dekuNukem/traffic-cone-film-scanning/images/dof35mm.png

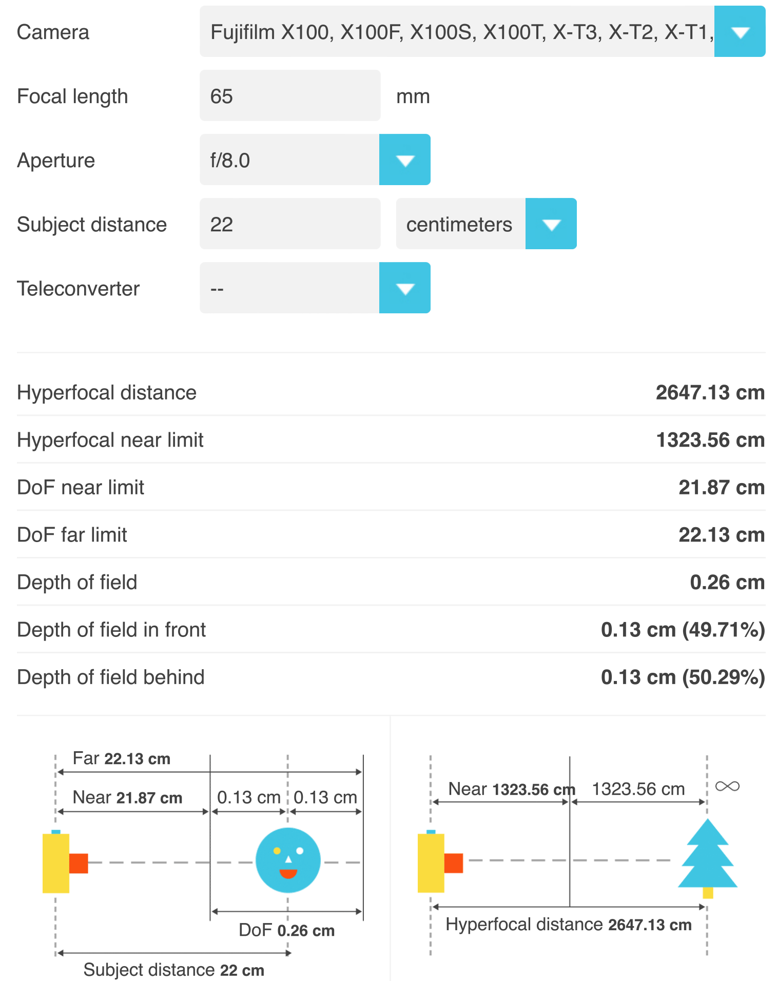
images/dof35mm.png
