dekuNukem/traffic-cone-film-scanning/images/dollaz.png

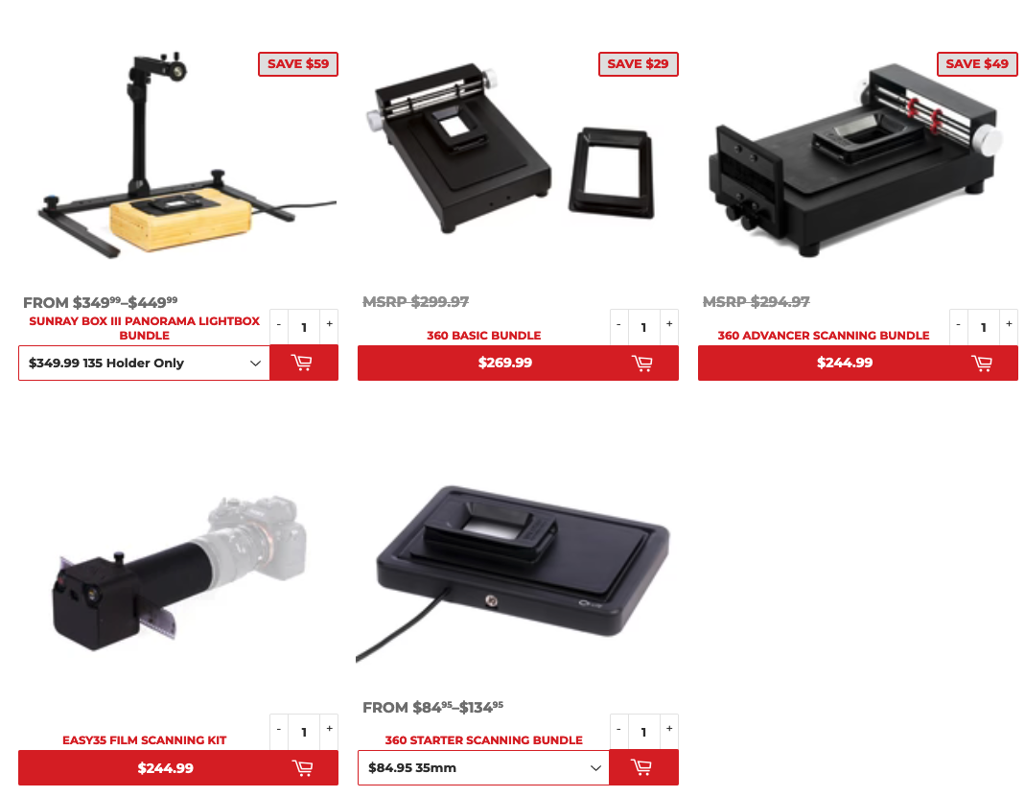
images/dollaz.png
