dekuNukem/traffic-cone-film-scanning/images/sw.jpg

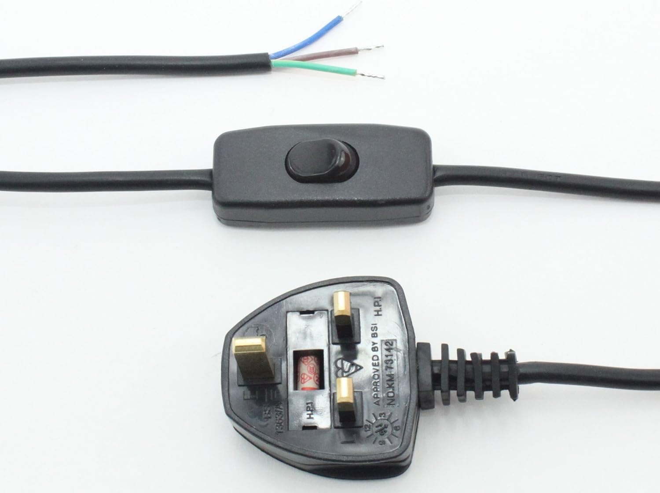
images/sw.jpg
